milagrofrost/Macintosh-PiForma-docs/stl/shelf/internal-three-level-rack.3mf

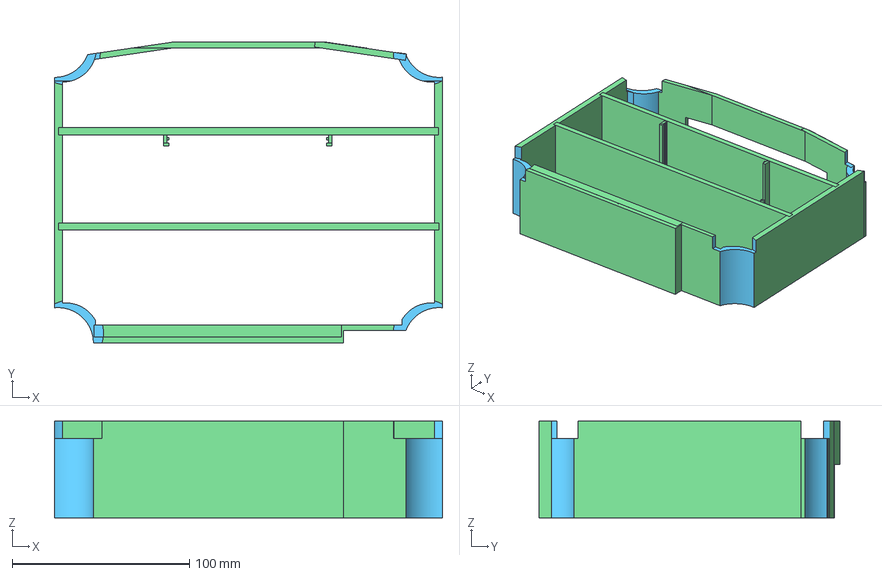
[picture p15: CAD file, 2026-07-16]
stl/shelf/internal-three-level-rack.3mf
219.0 x 170.0 x 54.5 mm
